appelis1965/Katsaronas-Stavros/code/Code/xbm.h

// WiFi ICON

// Espressif logo 50 x 50 pixel array in XBM format
#define logoWidth 32  // logo width
#define logoHeight 32 // logo height

// Image is stored in this array
PROGMEM const unsigned char logo[] = {
    0x00, 0x00, 0x00, 0x00, 0x00, 0x00, 0x00, 0x00, 0x00, 0x00, 0x00, 0x00,
    0x00, 0x00, 0x00, 0x00, 0x00, 0xA0, 0x05, 0x00, 0x00, 0xFE, 0x7F, 0x00,
    0x80, 0xFF, 0xFF, 0x01, 0xE0, 0xFF, 0xFF, 0x07, 0xF0, 0x0F, 0xF0, 0x1F,
    0xFC, 0x01, 0x80, 0x3F, 0x7E, 0x00, 0x00, 0x7E, 0x1E, 0x00, 0x00, 0x7C,
    0x0C, 0xE0, 0x0B, 0x30, 0x04, 0xFC, 0x3F, 0x20, 0x00, 0xFF, 0x7F, 0x00,
    0x80, 0xFF, 0xFF, 0x01, 0xC0, 0x1F, 0xF8, 0x03, 0xC0, 0x07, 0xE0, 0x03,
    0x00, 0x01, 0x80, 0x00, 0x00, 0x00, 0x00, 0x00, 0x00, 0xC0, 0x03, 0x00,
    0x00, 0xE0, 0x07, 0x00, 0x00, 0xE0, 0x07, 0x00, 0x00, 0xF0, 0x0F, 0x00,
    0x00, 0xF0, 0x0F, 0x00, 0x00, 0xE0, 0x07, 0x00, 0x00, 0xE0, 0x07, 0x00,
    0x00, 0x80, 0x01, 0x00, 0x00, 0x00, 0x00, 0x00, 0x00, 0x00, 0x00, 0x00,
    0x00, 0x00, 0x00, 0x00, 0x00, 0x00, 0x00, 0x00};

static unsigned char iot_icon[] = {
    0x00, 0x00, 0x00, 0x00, 0x10, 0x00, 0x00, 0x00, 0x30, 0x00, 0x00, 0x00,
    0x7c, 0x00, 0x00, 0x00, 0xfc, 0x00, 0x00, 0x00, 0xfc, 0x01, 0x00, 0x00,
    0xf8, 0x03, 0x00, 0x00, 0xf0, 0x07, 0x00, 0x00, 0xe0, 0x0f, 0x00, 0x00,
    0xc0, 0x1f, 0x00, 0x00, 0x80, 0x3f, 0x00, 0x00, 0x00, 0x3f, 0x00, 0x00,
    0x00, 0x9e, 0x03, 0x00, 0x00, 0xcc, 0x07, 0x00, 0x00, 0xe0, 0x0f, 0x00,
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
    0x3F,
    0xFC,
    0x3F,
    0xFE,
    0x7F,
    0xFE,
    0x3F,
    0xFE,
    0x7F,
    0xFE,
    0x3F,
    0xFF,
    0xFF,
    0xFE,
    0xBF,
    0xFF,
    0xFF,
    0xFE,
    0xBF,
    0xFF,
    0xFF,
    0xFF,
    0xBF,
    0xFF,
    0xFF,
    0xFE,
    0xBF,
    0xFF,
    0xFF,
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
};

static unsigned char plant_icon[] = {
    0x00,
    0x00,
    0x00,
    0x00,
    0x00,
    0x00,
    0x00,
    0x00,
    0x00,
    0x00,
    0x00,
    0xFC,
    0x00,
    0x00,
    0x80,
    0xFF,
    0x00,
    0x00,
    0xE0,
    0xFF,
    0x00,
    0x00,
    0xF0,
    0xE7,
    0x00,
    0x00,
    0xF8,
    0xE4,
    0x00,
    0x00,
    0x3C,
    0xEE,
    0x00,
    0x00,
    0x1C,
    0xEF,
    0xFE,
    0x07,
    0x9E,
    0x77,
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
};
